wybieracz/GMS-Firmware/src/AzIoTConfig.h

// Copyright (c) Microsoft Corporation. All rights reserved.
// SPDX-License-Identifier: MIT

#ifndef AZIOTCONFIG_H
#define AZIOTCONFIG_H

// Azure IoT
#define IOTHUB_FQDN ""
#define DEVICE_ID ""
#define DEVICE_KEY ""

// Publish 1 message every 5 seconds
#define TELEMETRY_FREQUENCY_MILLISECS 5000

#endif //AZIOTCONFIG_H
